AhmadTIM/MIPS-based-MCU-architecture/DUT/UART_TX.vhd

----------------------------------------------------------------------
-- File Downloaded from http://www.nandland.com
----------------------------------------------------------------------
-- This file contains the UART Transmitter.  This transmitter is able
-- to transmit 8 bits of serial data, one start bit, one stop bit,
-- and no parity bit.  When transmit is complete o_TX_Done will be
-- driven high for one clock cycle.
--
-- Set Generic g_CLKS_PER_BIT as follows:
-- g_CLKS_PER_BIT = (Frequency of i_Clk)/(Frequency of UART)
-- Example: 10 MHz Clock, 115200 baud UART
-- (10000000)/(115200) = 87
--
library ieee;
use ieee.std_logic_1164.all;
use ieee.numeric_std.all;
 
entity UART_TX is
  port (
    i_Clk       	: in  std_logic;
    i_TX_DV     	: in  std_logic;
    i_TX_Byte   	: in  std_logic_vector(7 downto 0);
    o_TX_Active 	: out std_logic; -- BUSY
    o_TX_Serial 	: out std_logic;
    o_TX_Done   	: out std_logic;
    SWRST       	: in  std_logic := '0'; -- Software reset enable
    PENA        	: in  std_logic := '0'; -- Parity enable
    g_CLKS_PER_BIT 	: in integer
    );
end UART_TX;
 
 
architecture RTL of UART_TX is
 
  type t_SM_Main is (s_Idle, s_TX_Start_Bit, s_TX_Data_Bits, 
                     s_TX_Parity, s_TX_Stop_Bit, s_Cleanup);
  signal r_SM_Main    : t_SM_Main := s_Idle;
 
  signal r_Clk_Count  : integer := 0;
  signal r_Bit_Index  : integer range 0 to 7 := 0;  -- 8 Bits Total
  signal r_TX_Data    : std_logic_vector(7 downto 0) := (others => '0');
  signal r_TX_Done    : std_logic := '0';
  signal TX_DV	      : std_logic := '0';
  signal parity_check : std_logic := '0';
   
begin
 
  p_UART_TX : process (i_Clk)
  begin
    if rising_edge(i_Clk) then
      if i_TX_DV = '0' then TX_DV <= '0'; else TX_DV <= '1'; end if;
      -- Software reset: clear everything
      if SWRST = '1' then
        r_SM_Main   <= s_Idle;
        r_Clk_Count <= 0;
        r_Bit_Index <= 0;
        r_TX_Done   <= '0';
        o_TX_Active <= '0';
        o_TX_Serial <= '1'; -- Idle line
      else
      
        case r_SM_Main is
 
          when s_Idle =>
            o_TX_Active <= '0';
            o_TX_Serial <= '1';         -- Drive Line High for Idle
            r_TX_Done   <= '0';
            r_Clk_Count <= 0;
            r_Bit_Index <= 0;
 
            if TX_DV = '1' then
              r_TX_Data <= i_TX_Byte;
              r_SM_Main <= s_TX_Start_Bit;
            else
              r_SM_Main <= s_Idle;
            end if;
 
          -- Send out Start Bit. Start bit = 0
          when s_TX_Start_Bit =>
            o_TX_Active <= '1';
            o_TX_Serial <= '0';
 
            if r_Clk_Count < g_CLKS_PER_BIT-1 then
              r_Clk_Count <= r_Clk_Count + 1;
            else
              r_Clk_Count <= 0;
              r_SM_Main   <= s_TX_Data_Bits;
            end if;
 
          -- Send Data Bits LSB-first
          when s_TX_Data_Bits =>
            o_TX_Serial <= r_TX_Data(r_Bit_Index);
           
            if r_Clk_Count < g_CLKS_PER_BIT-1 then
              r_Clk_Count <= r_Clk_Count + 1;
            else
              r_Clk_Count <= 0;
              if r_Bit_Index < 7 then
                r_Bit_Index <= r_Bit_Index + 1;
              else
                r_Bit_Index <= 0;
                if PENA = '1' then
                  r_SM_Main <= s_TX_Parity;
                else
                  r_SM_Main <= s_TX_Stop_Bit;
                end if;
              end if;
            end if;
 
          -- Send parity bit if enabled
          when s_TX_Parity =>
            o_TX_Serial <= parity_check;
            if r_Clk_Count < g_CLKS_PER_BIT-1 then
              r_Clk_Count <= r_Clk_Count + 1;
            else
              r_Clk_Count <= 0;
              r_SM_Main   <= s_TX_Stop_Bit;
            end if;
 
          -- Send out Stop bit. Stop bit = 1
          when s_TX_Stop_Bit =>
            o_TX_Serial <= '1';
            if r_Clk_Count < g_CLKS_PER_BIT-1 then
              r_Clk_Count <= r_Clk_Count + 1;
            else
              r_Clk_Count <= 0;
              r_SM_Main   <= s_Cleanup;
            end if;
 
          -- Cleanup, generate TX_Done pulse
          when s_Cleanup =>
            o_TX_Active <= '0';
            r_TX_Done   <= '1';    -- 1-cycle pulse
            r_SM_Main   <= s_Idle;
 
          when others =>
            r_SM_Main <= s_Idle;
 
        end case;
      end if;
    end if;
  end process p_UART_TX;
 
  o_TX_Done <= r_TX_Done;
 
  parity_check <= (i_TX_Byte(0) XOR i_TX_Byte(1) XOR i_TX_Byte(2) XOR i_TX_Byte(3) XOR
                   i_TX_Byte(4) XOR i_TX_Byte(5) XOR i_TX_Byte(6) XOR i_TX_Byte(7));
   
end RTL;
