AhmadTIM/MIPS-based-MCU-architecture/DUT/SevenSegDecoder.vhd

LIBRARY ieee;
USE ieee.std_logic_1164.all;
USE work.aux_package.all;
-------------------------------------
ENTITY SevenSegDecoder IS
  GENERIC (n: INTEGER := 4;
	   Size: integer := 7);
  PORT (input: in STD_LOGIC_VECTOR (n-1 DOWNTO 0);
	output: out STD_LOGIC_VECTOR (Size-1 downto 0));
END SevenSegDecoder;
--------------------------------------------------------------
ARCHITECTURE dfl OF SevenSegDecoder IS
BEGIN
	with input select
		output  <= 	"1000000" when "0000", -- 0
				"1111001" when "0001", -- 1
				"0100100" when "0010", -- 2
				"0110000" when "0011", -- 3
				"0011001" when "0100", -- 4
				"0010010" when "0101", -- 5
				"0000010" when "0110", -- 6
				"1111000" when "0111", -- 7 
				"0000000" when "1000", -- 8 
				"0010000" when "1001", -- 9
				"0001000" when "1010", -- A
				"0000011" when "1011", -- B
				"1000110" when "1100", -- C
				"0100001" when "1101", -- D
				"0000110" when "1110", -- E
				"0001110" when "1111", -- F
				"1111111" when others; -- None

					
END dfl;
